mattwach/epaper_clock/src/clock_number_font.c

// Generated font data for clock_number_font

#include <inttypes.h>
#include <avr/pgmspace.h> 

const uint8_t clock_number_font[] PROGMEM = {
    0x56, 0x41, 0x52, 0x31,  // id: VAR1
    0x0C, // num_chars
    0x0A, // height

    // Character offsets
    ' ', 40, 0x00, 0x30,  // off=48
    '0', 40, 0x00, 0x38,  // off=56
    '1', 40, 0x00, 0xED,  // off=237
    '2', 40, 0x01, 0x36,  // off=310
    '3', 40, 0x01, 0xCC,  // off=460
    '4', 40, 0x02, 0x7D,  // off=637
    '5', 40, 0x02, 0xEE,  // off=750
    '6', 40, 0x03, 0x7F,  // off=895
    '7', 40, 0x04, 0x47,  // off=1095
    '8', 40, 0x04, 0xA1,  // off=1185
    '9', 40, 0x05, 0x77,  // off=1399
    ':', 16, 0x06, 0x42,  // off=1602
    // Character data
    // Character 32 (0x20) ( )
    // ----------------------------------------
    // ----------------------------------------
    // ----------------------------------------
    // ----------------------------------------
    // ----------------------------------------
    // ----------------------------------------
    // ----------------------------------------
    // ----------------------------------------
    // ----------------------------------------
    // ----------------------------------------
    // ----------------------------------------
    // ----------------------------------------
    // ----------------------------------------
    // ----------------------------------------
    // ----------------------------------------
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
    // ----------------------------------------
    // ----------------------------------------
    // ----------------------------------------
    // ----------------------------------------
    // ----------------------------------------
    // ----------------------------------------
    0x0A, 0x00, 0x81, 0x80, 0x02, 0xC0, 0x03, 0xE0, 0x08, 0xF0, 0x03, 0xE0, 0x02, 0xC0, 0x81, 0x80,
    0x0F, 0x00, 0x84, 0x80, 0xF0, 0xF8, 0xFC, 0x04, 0xFF, 0x83, 0x7F, 0x3F, 0x1F, 0x07, 0x0F, 0x02,
    0x1F, 0x82, 0x3F, 0x7F, 0x04, 0xFF, 0x84, 0xFE, 0xFC, 0xF8, 0x80, 0x09, 0x00, 0x82, 0x7E, 0x7F,
    0x04, 0xFF, 0x82, 0x1F, 0x01, 0x10, 0x00, 0x81, 0x01, 0x06, 0xFF, 0x81, 0xFC, 0x1F, 0x00, 0x82,
    0x80, 0xC0, 0x05, 0xFF, 0x82, 0x3F, 0x07, 0x1A, 0x00, 0x85, 0x80, 0xC0, 0xF0, 0xF8, 0xFE, 0x03,
    0xFF, 0x84, 0x7F, 0x1F, 0x07, 0x03, 0x15, 0x00, 0x84, 0x80, 0xC0, 0xE0, 0xF0, 0x02, 0xFC, 0x03,
    0xFF, 0x02, 0x3F, 0x83, 0x0F, 0x07, 0x03, 0x14, 0x00, 0x85, 0x80, 0xC0, 0xF0, 0xF8, 0xFC, 0x03,
    0xFF, 0x86, 0x7F, 0x3F, 0x0F, 0x07, 0x03, 0x01, 0x15, 0x00, 0x85, 0x80, 0xE0, 0xF8, 0xFC, 0xFE,
    0x02, 0xFF, 0x85, 0x7F, 0x3F, 0x1F, 0x03, 0x01, 0x1B, 0x00, 0x81, 0xFC, 0x07, 0xFF, 0x19, 0xFC,
    0x07, 0x00, 0x21, 0x03, 0x04, 0x00,
    // Character 51 (0x33) (3)
    // ----------------------------------------
    // ----------------------------------------
    // ----------------------------------------
    // ----------------------------------------
    // ----------------########----------------
    // -------------##############-------------
    // -----------##################-----------
    // ----------####################----------
    // ---------######################---------
    // --------########################--------
    // -------##########################-------
    // ------############################------
    // ------##########--------##########------
    // ------########-----------#########------
    // -----#########------------########------
    // -----########--------------########-----
    // ----########----------------#######-----
    // ----#######------------------######-----
    // ----#######------------------#######----
    // ----#######------------------#######----
    // ----#######------------------#######----
    // ----######-------------------#######----
    // ------####-------------------#######----
    // -----------------------------#######----
    // -----------------------------#######----
    // -----------------------------#######----
    // -----------------------------######-----
    // -----------------------------######-----
    // -----------------------------######-----
    // ----------------------------######------
    // ---------------------------#######------
    // --------------------------########------
    // --------------------------#######-------
    // ------------------------########--------
    // ---------------------##########---------
    // ---------------################---------
    // ---------------###############----------
    // ---------------#############------------
    // ---------------###########--------------
    // ---------------#############------------
    // ---------------###############----------
    // ---------------################---------
    // ---------------#################--------
    // ----------------------############------
    // -------------------------#########------
    // --------------------------#########-----
    // ----------------------------#######-----
    // -----------------------------#######----
    // -----------------------------#######----
    // ------------------------------######----
    // ------------------------------######----
    // -------------------------------######---
    // -------------------------------######---
    // -------------------------------######---
    // -------------------------------######---
    // ------###----------------------######---
    // ---######----------------------######---
    // ---#######---------------------######---
    // ---#######---------------------######---
    // ----######--------------------#######---
    // ----#######-------------------######----
    // ----#######------------------#######----
    // ----#######------------------#######----
    // ----########-----------------#######----
    // -----#########-------------#########----
    // -----#########------------#########-----
    // ------##########--------###########-----
    // ------############################------
    // -------###########################------
    // --------#########################-------
    // ---------#######################--------
    // ---------######################---------
    // -----------##################-----------
    // -------------###############------------
    // ----------------#########---------------
    // ----------------------------------------
    // ----------------------------------------
    // ----------------------------------------
    // ----------------------------------------
    // ----------------------------------------
    0x0A, 0x00, 0x81, 0x80, 0x02, 0xC0, 0x03, 0xE0, 0x08, 0xF0, 0x03, 0xE0, 0x02, 0xC0, 0x81, 0x80,
    0x0F, 0x00, 0x84, 0xC0, 0xF8, 0xFC, 0xFE, 0x04, 0xFF, 0x81, 0x7F, 0x02, 0x1F, 0x08, 0x0F, 0x83,
    0x1F, 0x3F, 0x7F, 0x04, 0xFF, 0x84, 0xFE, 0xFC, 0xF8, 0x80, 0x09, 0x00, 0x02, 0x3F, 0x04, 0x7F,
    0x82, 0x1F, 0x01, 0x10, 0x00, 0x81, 0x01, 0x06, 0xFF, 0x81, 0xFC, 0x1E, 0x00, 0x83, 0x80, 0xC0,
    0xE0, 0x05, 0xFF, 0x82, 0x1F, 0x03, 0x13, 0x00, 0x06, 0xF8, 0x03, 0xFC, 0x02, 0xFE, 0x02, 0xBF,
    0x02, 0x1F, 0x83, 0x0F, 0x03, 0x01, 0x16, 0x00, 0x07, 0x07, 0x03, 0x0F, 0x81, 0x1F, 0x02, 0x3F,
    0x84, 0x7F, 0xFF, 0xFE, 0xFC, 0x02, 0xF8, 0x82, 0xE0, 0x80, 0x0A, 0x00, 0x03, 0x80, 0x14, 0x00,
    0x82, 0x01, 0x07, 0x05, 0xFF, 0x81, 0xF8, 0x06, 0x00, 0x81, 0x07, 0x05, 0xFF, 0x83, 0xFE, 0xF0,
    0x80, 0x11, 0x00, 0x82, 0xE0, 0xF8, 0x05, 0xFF, 0x81, 0x0F, 0x08, 0x00, 0x84, 0x03, 0x0F, 0x1F,
    0x3F, 0x05, 0xFF, 0x02, 0xFC, 0x08, 0xF8, 0x02, 0xFC, 0x81, 0xFE, 0x04, 0xFF, 0x85, 0x7F, 0x3F,
    0x1F, 0x07, 0x01, 0x0F, 0x00, 0x02, 0x01, 0x03, 0x03, 0x09, 0x07, 0x03, 0x03, 0x81, 0x01, 0x0B,
    0x00,
    // Character 52 (0x34) (4)
    // ----------------------------------------
    // ----------------------------------------
    // ----------------------------------------
    // ----------------------------------------
    // ----------------------------------------
    // ------------------------#######---------
    // ------------------------#######---------
    // -----------------------########---------
    // -----------------------########---------
    // ----------------------#########---------
    // ---------------------##########---------
    // ---------------------##########---------
    // ---------------------##########---------
    // --------------------###########---------
    // -------------------############---------
    // -------------------############---------
    // -------------------#####-######---------
    // ------------------######-######---------
    // -----------------######--######---------
    // -----------------######--######---------
    // ----------------######---######---------
    // ----------------#####----######---------
    // ----------------#####----######---------
    // ---------------######----######---------
    // --------------######-----######---------
    // --------------#####------######---------
    // --------------#####------######---------
    // -------------######------######---------
    // ------------######-------######---------
    // ------------######-------######---------
    // -----------######--------######---------
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
    0x02, 0x3F, 0x81, 0x7F, 0x05, 0xFF, 0x84, 0xFC, 0xF8, 0xF0, 0xC0, 0x09, 0x00, 0x07, 0x03, 0x81,
    0x01, 0x0F, 0x00, 0x84, 0x01, 0x03, 0x1F, 0x7F, 0x05, 0xFF, 0x81, 0xC0, 0x22, 0x00, 0x06, 0xFF,
    0x06, 0x00, 0x81, 0x0C, 0x02, 0xFC, 0x03, 0xFE, 0x83, 0xF8, 0xE0, 0x80, 0x0F, 0x00, 0x83, 0x80,
    0xC0, 0xF8, 0x05, 0xFF, 0x81, 0x7F, 0x08, 0x00, 0x85, 0x01, 0x07, 0x1F, 0x3F, 0x7F, 0x04, 0xFF,
    0x81, 0xFE, 0x02, 0xFC, 0x07, 0xF8, 0x02, 0xFC, 0x81, 0xFE, 0x03, 0xFF, 0x02, 0x7F, 0x84, 0x1F,
    0x0F, 0x07, 0x01, 0x10, 0x00, 0x81, 0x01, 0x03, 0x03, 0x09, 0x07, 0x02, 0x03, 0x03, 0x01, 0x0B,
    0x00,
    // Character 54 (0x36) (6)
    // ----------------------------------------
    // ----------------------------------------
    // ----------------------------------------
    // ----------------------------------------
    // ------------------########--------------
    // ----------------############------------
    // --------------###############-----------
    // -------------##################---------
    // -----------####################---------
    // -----------#####################--------
    // ----------#######################-------
    // ---------#########################------
    // ---------##########-----##########------
    // ---------#######----------########------
    // --------#######-----------#########-----
    // -------#######-------------########-----
    // -------#######--------------#######-----
    // ------#######----------------#######----
    // ------#######----------------#######----
    // ------######-----------------##---------
    // ------#####-----------------------------
    // ------#####-----------------------------
    // -----######-----------------------------
    // -----######-----------------------------
    // -----######-----------------------------
    // -----######-----------------------------
    // ----######------------------------------
    // ----######------------------------------
    // ----######------------------------------
    // ----######---------#######--------------
    // ----######------############------------
    // ----#####-----###############-----------
    // ----#####----##################---------
    // ----#####---###################---------
    // ----#####--######################-------
    // ----#####--#######################------
    // ----#####-########################------
    // ----#####-#######-------##########------
    // ----###########-----------#########-----
    // ----##########------------#########-----
    // ----#########---------------########----
    // ----########-----------------#######----
    // ----#######------------------#######----
    // ----#######------------------#######----
    // ----#######-------------------######----
    // ----#######-------------------######----
    // ----######--------------------#######---
    // ----######---------------------######---
    // ----######---------------------######---
    // ----######---------------------######---
    // ----######---------------------######---
    // ----######---------------------######---
    // ----######---------------------######---
    // ----######---------------------######---
    // ----#######--------------------######---
    // -----######--------------------######---
    // -----######-------------------#######---
    // -----######-------------------######----
    // -----######-------------------######----
    // ------#####------------------#######----
    // ------######-----------------#######----
    // ------#######----------------#######----
    // ------########--------------########----
    // -------#######--------------#######-----
    // -------########-----------#########-----
    // --------########----------########------
    // --------##########------##########------
    // ---------#########################------
    // ---------########################-------
    // ----------######################--------
    // -----------####################---------
    // ------------##################----------
    // -------------################-----------
    // ---------------############-------------
    // -----------------########---------------
    // ----------------------------------------
    // ----------------------------------------
    // ----------------------------------------
    // ----------------------------------------
    // ----------------------------------------
    0x0D, 0x00, 0x81, 0x80, 0x02, 0xC0, 0x02, 0xE0, 0x08, 0xF0, 0x02, 0xE0, 0x81, 0xC0, 0x02, 0x80,
    0x10, 0x00, 0x84, 0x80, 0xC0, 0xF8, 0xFC, 0x03, 0xFF, 0x82, 0x7F, 0x3F, 0x03, 0x1F, 0x05, 0x0F,
    0x02, 0x1F, 0x81, 0x7F, 0x04, 0xFF, 0x84, 0xFE, 0xFC, 0xF8, 0xC0, 0x0A, 0x00, 0x82, 0xC0, 0xFE,
    0x04, 0xFF, 0x83, 0x0F, 0x07, 0x01, 0x0E, 0x00, 0x81, 0x01, 0x02, 0x0F, 0x04, 0x07, 0x81, 0x06,
    0x08, 0x00, 0x81, 0xFC, 0x04, 0xFF, 0x82, 0x7F, 0x03, 0x03, 0x00, 0x02, 0x80, 0x03, 0xC0, 0x07,
    0xE0, 0x02, 0xC0, 0x81, 0x80, 0x0F, 0x00, 0x05, 0xFF, 0x86, 0xC0, 0xF0, 0xFC, 0xFE, 0xFF, 0x7F,
    0x02, 0x3F, 0x07, 0x1F, 0x02, 0x3F, 0x05, 0xFF, 0x02, 0xFC, 0x82, 0xF8, 0xC0, 0x09, 0x00, 0x06,
    0xFF, 0x83, 0x3F, 0x03, 0x01, 0x0F, 0x00, 0x83, 0x01, 0x0F, 0x7F, 0x05, 0xFF, 0x81, 0xC0, 0x07,
    0x00, 0x81, 0x7F, 0x05, 0xFF, 0x81, 0xC0, 0x14, 0x00, 0x06, 0xFF, 0x08, 0x00, 0x82, 0x07, 0x7F,
    0x04, 0xFF, 0x83, 0xF0, 0xE0, 0xC0, 0x0E, 0x00, 0x82, 0xC0, 0xF8, 0x05, 0xFF, 0x82, 0x7F, 0x01,
    0x0A, 0x00, 0x85, 0x01, 0x07, 0x1F, 0x3F, 0x7F, 0x03, 0xFF, 0x81, 0xFE, 0x02, 0xFC, 0x06, 0xF8,
    0x02, 0xFC, 0x04, 0xFF, 0x85, 0x7F, 0x3F, 0x1F, 0x0F, 0x01, 0x12, 0x00, 0x02, 0x01, 0x02, 0x03,
    0x08, 0x07, 0x02, 0x03, 0x02, 0x01, 0x0B, 0x00,
    // Character 55 (0x37) (7)
    // ----------------------------------------
    // ----------------------------------------
    // ----------------------------------------
    // ----------------------------------------
    // ----------------------------------------
    // ----################################----
    // ----################################----
    // ----################################----
    // ----################################----
    // ----################################----
    // ----################################----
    // ----################################----
    // ----################################----
    // ------------------------------######----
    // -----------------------------#######----
    // -----------------------------######-----
    // -----------------------------#####------
    // ----------------------------######------
    // ---------------------------#######------
    // ---------------------------######-------
    // --------------------------#######-------
    // --------------------------######--------
    // --------------------------######--------
    // -------------------------######---------
    // ------------------------#######---------
    // ------------------------#######---------
    // ------------------------######----------
    // ------------------------######----------
    // -----------------------######-----------
    // -----------------------######-----------
    // ----------------------#######-----------
    // ---------------------#######------------
    // ---------------------#######------------
    // ---------------------######-------------
    // ---------------------######-------------
    // --------------------######--------------
    // --------------------######--------------
    // -------------------#######--------------
    // -------------------#######--------------
    // -------------------######---------------
    // -------------------######---------------
    // -------------------######---------------
    // ------------------######----------------
    // ------------------######----------------
    // -----------------#######----------------
    // -----------------#######----------------
    // -----------------######-----------------
    // ----------------#######-----------------
    // ----------------#######-----------------
    // ----------------######------------------
    // ----------------######------------------
    // ----------------######------------------
    // ---------------######-------------------
    // ---------------######-------------------
    // ---------------######-------------------
    // ---------------######-------------------
    // --------------#######-------------------
    // --------------#######-------------------
    // --------------#######-------------------
    // --------------#######-------------------
    // --------------######--------------------
    // --------------######--------------------
    // --------------######--------------------
    // --------------######--------------------
    // --------------######--------------------
    // --------------######--------------------
    // -------------######---------------------
    // -------------######---------------------
    // -------------######---------------------
    // -------------######---------------------
    // -------------######---------------------
    // -------------######---------------------
    // -------------######---------------------
    // -------------######---------------------
    // ----------------------------------------
    // ----------------------------------------
    // ----------------------------------------
    // ----------------------------------------
    // ----------------------------------------
    // ----------------------------------------
    0x04, 0x00, 0x20, 0xE0, 0x08, 0x00, 0x19, 0x1F, 0x81, 0xDF, 0x05, 0xFF, 0x81, 0x7F, 0x1D, 0x00,
    0x84, 0x80, 0xF0, 0xFC, 0xFE, 0x02, 0xFF, 0x83, 0x7F, 0x1F, 0x07, 0x1B, 0x00, 0x83, 0x80, 0xC0,
    0xF0, 0x04, 0xFF, 0x83, 0x7F, 0x0F, 0x03, 0x1C, 0x00, 0x82, 0xE0, 0xF8, 0x04, 0xFF, 0x83, 0x7F,
    0x07, 0x01, 0x1C, 0x00, 0x83, 0x80, 0xF0, 0xFC, 0x04, 0xFF, 0x82, 0x3F, 0x03, 0x1E, 0x00, 0x81,
    0xF0, 0x05, 0xFF, 0x82, 0x0F, 0x01, 0x1F, 0x00, 0x06, 0xFF, 0x81, 0x0F, 0x20, 0x00, 0x81, 0xFC,
    0x05, 0xFF, 0x81, 0x03, 0x21, 0x00, 0x06, 0x03, 0x15, 0x00,
    // Character 56 (0x38) (8)
    // ----------------------------------------
    // ----------------------------------------
    // ----------------------------------------
    // ----------------------------------------
    // ----------------########----------------
    // -------------##############-------------
    // -----------##################-----------
    // ----------####################----------
    // ---------######################---------
    // --------########################--------
    // -------##########################-------
    // -------##########################-------
    // ------##########--------##########------
    // ------########------------########------
    // ------########------------########------
    // -----########--------------########-----
    // -----#######----------------#######-----
    // -----######------------------######-----
    // ----#######------------------#######----
    // ----#######------------------#######----
    // ----#######------------------#######----
    // ----#######------------------#######----
    // ----#######------------------#######----
    // ----#######------------------#######----
    // ----#######------------------#######----
    // ----#######------------------#######----
    // -----######------------------######-----
    // -----######------------------######-----
    // -----######------------------######-----
    // ------######----------------######------
    // ------#######--------------#######------
    // ------########------------########------
    // -------########-----------#######-------
    // -------#########--------#########-------
    // --------########################--------
    // ---------######################---------
    // ----------####################----------
    // -----------#################------------
    // ------------################------------
    // ----------####################----------
    // ---------######################---------
    // --------#########################-------
    // ------##########--------##########------
    // ------########------------########------
    // -----########--------------########-----
    // -----#######-----------------######-----
    // ----#######------------------#######----
    // ----#######------------------#######----
    // ----######--------------------######----
    // ----######--------------------######----
    // ---#######---------------------######---
    // ---######----------------------######---
    // ---######----------------------######---
    // ---######----------------------######---
    // ---######----------------------######---
    // ---######----------------------######---
    // ---######----------------------######---
    // ---######----------------------######---
    // ---#######--------------------#######---
    // ---#######--------------------#######---
    // ----######--------------------######----
    // ----#######------------------#######----
    // ----#######------------------#######----
    // ----########-----------------#######----
    // ----#########--------------#########----
    // -----#########------------#########-----
    // -----###########--------###########-----
    // ------############################------
    // ------############################------
    // -------##########################-------
    // --------########################--------
    // ---------######################---------
    // -----------##################-----------
    // ------------################------------
    // ----------------########----------------
    // ----------------------------------------
    // ----------------------------------------
    // ----------------------------------------
    // ----------------------------------------
    // ----------------------------------------
    0x0A, 0x00, 0x81, 0x80, 0x02, 0xC0, 0x03, 0xE0, 0x08, 0xF0, 0x03, 0xE0, 0x02, 0xC0, 0x81, 0x80,
    0x0F, 0x00, 0x84, 0x80, 0xF0, 0xFC, 0xFE, 0x04, 0xFF, 0x81, 0x7F, 0x02, 0x1F, 0x08, 0x0F, 0x02,
    0x1F, 0x81, 0x7F, 0x04, 0xFF, 0x84, 0xFE, 0xFC, 0xF0, 0x80, 0x09, 0x00, 0x81, 0xFC, 0x06, 0xFF,
    0x81, 0x01, 0x10, 0x00, 0x81, 0x01, 0x06, 0xFF, 0x81, 0xFC, 0x08, 0x00, 0x82, 0x03, 0x1F, 0x05,
    0xFF, 0x83, 0xE0, 0xC0, 0x80, 0x0C, 0x00, 0x83, 0x80, 0xC0, 0xE0, 0x05, 0xFF, 0x82, 0x1F, 0x03,
    0x0B, 0x00, 0x85, 0x03, 0x07, 0x0F, 0x9F, 0xBF, 0x03, 0xFF, 0x81, 0xFE, 0x08, 0xFC, 0x02, 0xFE,
    0x02, 0xFF, 0x02, 0x9F, 0x83, 0x0F, 0x07, 0x03, 0x0B, 0x00, 0x82, 0xC0, 0xF0, 0x02, 0xFC, 0x81,
    0xFE, 0x02, 0xFF, 0x83, 0x3F, 0x1F, 0x0F, 0x02, 0x07, 0x08, 0x03, 0x02, 0x07, 0x81, 0x0F, 0x02,
    0x1F, 0x02, 0xFF, 0x02, 0xFE, 0x83, 0xFC, 0xF0, 0xC0, 0x07, 0x00, 0x81, 0xFC, 0x05, 0xFF, 0x81,
    0x07, 0x14, 0x00, 0x81, 0x03, 0x05, 0xFF, 0x81, 0xFC, 0x06, 0x00, 0x81, 0x0F, 0x05, 0xFF, 0x83,
    0xFC, 0xE0, 0x80, 0x11, 0x00, 0x82, 0xE0, 0xFC, 0x05, 0xFF, 0x81, 0x0F, 0x07, 0x00, 0x85, 0x01,
    0x07, 0x1F, 0x3F, 0x7F, 0x04, 0xFF, 0x81, 0xFE, 0x02, 0xFC, 0x08, 0xF8, 0x02, 0xFC, 0x81, 0xFE,
    0x04, 0xFF, 0x85, 0x7F, 0x3F, 0x1F, 0x07, 0x01, 0x0F, 0x00, 0x81, 0x01, 0x04, 0x03, 0x08, 0x07,
    0x04, 0x03, 0x81, 0x01, 0x0B, 0x00,
    // Character 57 (0x39) (9)
    // ----------------------------------------
    // ----------------------------------------
    // ----------------------------------------
    // ----------------------------------------
    // ----------------########----------------
    // -------------#############--------------
    // -----------################-------------
    // ----------###################-----------
    // ---------####################-----------
    // --------######################----------
    // -------########################---------
    // ------#########################---------
    // ------##########------##########--------
    // ------########----------#########-------
    // -----#########-----------########-------
    // ----########--------------########------
    // ----#######----------------#######------
    // ----#######----------------#######------
    // ----#######-----------------######------
    // ----#######------------------#####------
    // ----######-------------------######-----
    // ---#######-------------------######-----
    // ---#######-------------------######-----
    // ---######--------------------#######----
    // ---######---------------------######----
    // ---######---------------------######----
    // ---######---------------------######----
    // ---######---------------------######----
    // ---######---------------------######----
    // ---######---------------------######----
    // ---######---------------------######----
    // ---#######--------------------######----
    // ---#######--------------------######----
    // ----######-------------------#######----
    // ----#######------------------#######----
    // ----#######------------------#######----
    // ----#######------------------#######----
    // ----########----------------########----
    // ----########---------------#########----
    // -----#########------------##########----
    // -----#########----------############----
    // ------##########------########-#####----
    // ------#######################--#####----
    // -------######################--#####----
    // --------#####################--#####----
    // ---------##################----#####----
    // ---------#################----######----
    // -----------##############-----######----
    // ------------############------######----
    // --------------#######---------######----
    // ------------------------------######----
    // ------------------------------######----
    // -----------------------------#######----
    // -----------------------------######-----
    // -----------------------------######-----
    // -----------------------------######-----
    // -----------------------------######-----
    // -----------------------------#####------
    // ----------------------------######------
    // --------##------------------######------
    // ----#######----------------#######------
    // ----#######---------------########------
    // ----#######---------------#######-------
    // ----########-------------#######--------
    // ----#########-----------########--------
    // -----#########---------########---------
    // ------##########-----##########---------
    // ------#########################---------
    // ------########################----------
    // -------######################-----------
    // --------####################------------
    // ---------##################-------------
    // ----------################--------------
    // -----------#############----------------
    // --------------########------------------
    // ----------------------------------------
    // ----------------------------------------
    // ----------------------------------------
    // ----------------------------------------
    // ----------------------------------------
    0x0A, 0x00, 0x81, 0x80, 0x02, 0xC0, 0x03, 0xE0, 0x08, 0xF0, 0x02, 0xE0, 0x81, 0xC0, 0x02, 0x80,
    0x0F, 0x00, 0x85, 0x80, 0xC0, 0xF8, 0xFC, 0xFE, 0x03, 0xFF, 0x02, 0x7F, 0x02, 0x1F, 0x06, 0x0F,
    0x02, 0x1F, 0x82, 0x3F, 0x7F, 0x03, 0xFF, 0x85, 0xFE, 0xFC, 0xF0, 0xE0, 0x80, 0x09, 0x00, 0x81,
    0xE0, 0x05, 0xFF, 0x82, 0x7F, 0x0F, 0x10, 0x00, 0x82, 0x03, 0x07, 0x05, 0xFF, 0x82, 0xF0, 0x80,
    0x07, 0x00, 0x06, 0xFF, 0x81, 0x80, 0x14, 0x00, 0x06, 0xFF, 0x07, 0x00, 0x82, 0x01, 0x7F, 0x05,
    0xFF, 0x82, 0xFC, 0xE0, 0x02, 0x80, 0x0C, 0x00, 0x84, 0x80, 0xC0, 0xE0, 0xFE, 0x06, 0xFF, 0x09,
    0x00, 0x84, 0x01, 0x07, 0x0F, 0x1F, 0x02, 0x7F, 0x03, 0xFF, 0x02, 0xFE, 0x06, 0xFC, 0x02, 0xFE,
    0x83, 0xFF, 0x7F, 0x3F, 0x02, 0x1F, 0x82, 0x03, 0xC1, 0x05, 0xFF, 0x10, 0x00, 0x02, 0x01, 0x07,
    0x03, 0x03, 0x01, 0x05, 0x00, 0x81, 0xF0, 0x05, 0xFF, 0x81, 0x1F, 0x08, 0x00, 0x04, 0xF0, 0x02,
    0xF8, 0x82, 0xF0, 0x80, 0x0D, 0x00, 0x84, 0x80, 0xE0, 0xF0, 0xFC, 0x03, 0xFF, 0x83, 0x7F, 0x3F,
    0x01, 0x09, 0x00, 0x85, 0x01, 0x03, 0x1F, 0x3F, 0x7F, 0x04, 0xFF, 0x81, 0xFE, 0x02, 0xFC, 0x05,
    0xF8, 0x02, 0xFC, 0x81, 0xFE, 0x03, 0xFF, 0x85, 0x7F, 0x3F, 0x1F, 0x0F, 0x01, 0x12, 0x00, 0x81,
    0x01, 0x03, 0x03, 0x08, 0x07, 0x02, 0x03, 0x02, 0x01, 0x0E, 0x00,
    // Character 58 (0x3A) (:)
    // ----------------
    // ----------------
    // ----------------
    // ----------------
    // ----------------
    // ----------------
    // ----------------
    // ----------------
    // ----------------
    // ----------------
    // ----------------
    // ----------------
    // ----------------
    // ----------------
    // ----------------
    // ----------------
    // ----------------
    // ----------------
    // ----------------
    // ---#########----
    // ---#########----
    // ---#########----
    // ---#########----
    // ---#########----
    // ---#########----
    // ---#########----
    // ---#########----
    // ---#########----
    // ---#########----
    // ---#########----
    // ---#########----
    // ---#########----
    // ---#########----
    // ---#########----
    // ----------------
    // ----------------
    // ----------------
    // ----------------
    // ----------------
    // ----------------
    // ----------------
    // ----------------
    // ----------------
    // ----------------
    // ----------------
    // ----------------
    // ----------------
    // ----------------
    // ----------------
    // ----------------
    // ----------------
    // ----------------
    // ----------------
    // ----------------
    // ----------------
    // ----------------
    // ----------------
    // ----------------
    // ----------------
    // ---#########----
    // ---#########----
    // ---#########----
    // ---#########----
    // ---#########----
    // ---#########----
    // ---#########----
    // ---#########----
    // ---#########----
    // ---#########----
    // ---#########----
    // ---#########----
    // ---#########----
    // ---#########----
    // ---#########----
    // ----------------
    // ----------------
    // ----------------
    // ----------------
    // ----------------
    // ----------------
    0x23, 0x00, 0x09, 0xF8, 0x07, 0x00, 0x09, 0xFF, 0x07, 0x00, 0x09, 0x03, 0x27, 0x00, 0x09, 0xF8,
    0x07, 0x00, 0x09, 0xFF, 0x07, 0x00, 0x09, 0x03, 0x04, 0x00,
};
