mattwach/epaper_clock/src/labels_font.c

// Generated font data for labels_font

#include <inttypes.h>
#include <avr/pgmspace.h> 

const uint8_t labels_font[] PROGMEM = {
    0x56, 0x41, 0x52, 0x31,  // id: VAR1
    0x11, // num_chars
    0x03, // height

    // Character offsets
    ' ', 9, 0x00, 0x44,  // off=68
    '%', 19, 0x00, 0x46,  // off=70
    '.', 6, 0x00, 0x7D,  // off=125
    '/', 8, 0x00, 0x83,  // off=131
    ':', 6, 0x00, 0x97,  // off=151
    'A', 14, 0x00, 0xA1,  // off=161
    'C', 15, 0x00, 0xBE,  // off=190
    'F', 12, 0x00, 0xE5,  // off=229
    'H', 12, 0x00, 0xF7,  // off=247
    'M', 15, 0x01, 0x11,  // off=273
    'P', 13, 0x01, 0x3D,  // off=317
    'T', 14, 0x01, 0x56,  // off=342
    'U', 14, 0x01, 0x68,  // off=360
    'h', 11, 0x01, 0x88,  // off=392
    'i', 5, 0x01, 0xA2,  // off=418
    'n', 11, 0x01, 0xB0,  // off=432
    'r', 8, 0x01, 0xC6,  // off=454
    // Character data
    // Character 32 (0x20) ( )
    // ---------
    // ---------
    // ---------
    // ---------
    // ---------
    // ---------
    // ---------
    // ---------
    // ---------
    // ---------
    // ---------
    // ---------
    // ---------
    // ---------
    // ---------
    // ---------
    // ---------
    // ---------
    // ---------
    // ---------
    // ---------
    // ---------
    // ---------
    // ---------
    0x1B, 0x00,
    // Character 37 (0x25) (%)
    // -------------------
    // -------------------
    // -------------------
    // -------------------
    // -------------------
    // -------------------
    // --####-------##----
    // -##--##-----##-----
    // -#----#-----#------
    // -#----#----##------
    // -#----#---##-------
    // -#----#---#--------
    // -##--##--##--####--
    // --####--##--##--##-
    // --------#---#----#-
    // -------##---#----#-
    // ------##----#----#-
    // ------#-----#----#-
    // -----##-----##--##-
    // ----##-------####--
    // -------------------
    // -------------------
    // -------------------
    // -------------------
    0x83, 0x00, 0x80, 0xC0, 0x02, 0x40, 0x82, 0xC0, 0x80, 0x05, 0x00, 0x83, 0x80, 0xC0, 0x40, 0x05,
    0x00, 0x82, 0x1F, 0x30, 0x02, 0x20, 0x89, 0x30, 0x1F, 0x80, 0xE0, 0x30, 0x1C, 0x06, 0xE3, 0x30,
    0x02, 0x10, 0x82, 0x30, 0xE0, 0x05, 0x00, 0x84, 0x08, 0x0C, 0x07, 0x01, 0x04, 0x00, 0x82, 0x07,
    0x0C, 0x02, 0x08, 0x83, 0x0C, 0x07, 0x00,
    // Character 46 (0x2E) (.)
    // ------
    // ------
    // ------
    // ------
    // ------
    // ------
    // ------
    // ------
    // ------
    // ------
    // ------
    // ------
    // ------
    // ------
    // ------
    // ------
    // ------
    // ------
    // --##--
    // --##--
    // ------
    // ------
    // ------
    // ------
    0x0E, 0x00, 0x02, 0x0C, 0x02, 0x00,
    // Character 47 (0x2F) (/)
    // --------
    // --------
    // --------
    // --------
    // --------
    // -----##-
    // -----##-
    // -----#--
    // ----##--
    // ----##--
    // ----#---
    // ---##---
    // ---##---
    // ---##---
    // ---#----
    // --##----
    // --##----
    // --#-----
    // -##-----
    // -##-----
    // --------
    // --------
    // --------
    // --------
    0x05, 0x00, 0x82, 0xE0, 0x60, 0x03, 0x00, 0x84, 0x80, 0xF8, 0x3F, 0x03, 0x03, 0x00, 0x83, 0x0C,
    0x0F, 0x01, 0x04, 0x00,
    // Character 58 (0x3A) (:)
    // ------
    // ------
    // ------
    // ------
    // ------
    // ------
    // ------
    // ------
    // ------
    // --##--
    // --##--
    // ------
    // ------
    // ------
    // ------
    // ------
    // ------
    // ------
    // --##--
    // --##--
    // ------
    // ------
    // ------
    // ------
    0x08, 0x00, 0x02, 0x06, 0x04, 0x00, 0x02, 0x0C, 0x02, 0x00,
    // Character 65 (0x41) (A)
    // --------------
    // --------------
    // --------------
    // --------------
    // --------------
    // --------------
    // -----###------
    // -----###------
    // ----##-##-----
    // ----##-##-----
    // ----#---#-----
    // ---##---##----
    // ---##---##----
    // ---#-----#----
    // --#########---
    // --#-------#---
    // -##-------##--
    // -##-------##--
    // -##--------#--
    // ##---------##-
    // --------------
    // --------------
    // --------------
    // --------------
    0x05, 0x00, 0x03, 0xC0, 0x08, 0x00, 0x89, 0xC0, 0x78, 0x5F, 0x43, 0x40, 0x43, 0x5F, 0x78, 0xC0,
    0x03, 0x00, 0x83, 0x08, 0x0F, 0x07, 0x07, 0x00, 0x84, 0x03, 0x0F, 0x08, 0x00,
    // Character 67 (0x43) (C)
    // ---------------
    // ---------------
    // ---------------
    // ---------------
    // ---------------
    // ---------------
    // -----######----
    // ---###----###--
    // --##-------###-
    // --##--------##-
    // -##------------
    // -##------------
    // -##------------
    // -##------------
    // -##------------
    // -##------------
    // --##--------##-
    // --###-------##-
    // ---###----###--
    // -----######----
    // ---------------
    // ---------------
    // ---------------
    // ---------------
    0x03, 0x00, 0x02, 0x80, 0x81, 0xC0, 0x04, 0x40, 0x81, 0xC0, 0x02, 0x80, 0x03, 0x00, 0x83, 0xFC,
    0xFF, 0x03, 0x07, 0x00, 0x81, 0x01, 0x02, 0x03, 0x03, 0x00, 0x84, 0x03, 0x07, 0x06, 0x0C, 0x04,
    0x08, 0x85, 0x0C, 0x04, 0x07, 0x03, 0x00,
    // Character 70 (0x46) (F)
    // ------------
    // ------------
    // ------------
    // ------------
    // ------------
    // ------------
    // -##########-
    // -##---------
    // -##---------
    // -##---------
    // -##---------
    // -##---------
    // -##---------
    // -##########-
    // -##---------
    // -##---------
    // -##---------
    // -##---------
    // -##---------
    // -##---------
    // ------------
    // ------------
    // ------------
    // ------------
    0x81, 0x00, 0x02, 0xC0, 0x08, 0x40, 0x02, 0x00, 0x02, 0xFF, 0x08, 0x20, 0x02, 0x00, 0x02, 0x0F,
    0x09, 0x00,
    // Character 72 (0x48) (H)
    // ------------
    // ------------
    // ------------
    // ------------
    // ------------
    // ------------
    // -##------##-
    // -##------##-
    // -##------##-
    // -##------##-
    // -##------##-
    // -##------##-
    // -##########-
    // -##------##-
    // -##------##-
    // -##------##-
    // -##------##-
    // -##------##-
    // -##------##-
    // -##------##-
    // ------------
    // ------------
    // ------------
    // ------------
    0x81, 0x00, 0x02, 0xC0, 0x06, 0x00, 0x02, 0xC0, 0x02, 0x00, 0x02, 0xFF, 0x06, 0x10, 0x02, 0xFF,
    0x02, 0x00, 0x02, 0x0F, 0x06, 0x00, 0x02, 0x0F, 0x01, 0x00,
    // Character 77 (0x4D) (M)
    // ---------------
    // ---------------
    // ---------------
    // ---------------
    // ---------------
    // ---------------
    // -##---------##-
    // -###-------###-
    // -#-#-------#-#-
    // -#-##------#-#-
    // -#-##-----##-#-
    // -#--#-----#--#-
    // -#--##---##--#-
    // -#--##---##--#-
    // -#---##--#---#-
    // -#---##-##---#-
    // -#----#-##---#-
    // -#----#-#----#-
    // -#----###----#-
    // -#-----#-----#-
    // ---------------
    // ---------------
    // ---------------
    // ---------------
    0x81, 0x00, 0x02, 0xC0, 0x81, 0x80, 0x07, 0x00, 0x81, 0x80, 0x02, 0xC0, 0x02, 0x00, 0x8D, 0xFF,
    0x00, 0x07, 0x3E, 0xF0, 0xC0, 0x00, 0x80, 0xF0, 0x3C, 0x07, 0x00, 0xFF, 0x02, 0x00, 0x81, 0x0F,
    0x04, 0x00, 0x84, 0x07, 0x0C, 0x07, 0x01, 0x03, 0x00, 0x82, 0x0F, 0x00,
    // Character 80 (0x50) (P)
    // -------------
    // -------------
    // -------------
    // -------------
    // -------------
    // -------------
    // -#########---
    // -##------##--
    // -##-------##-
    // -##-------##-
    // -##-------##-
    // -##-------##-
    // -##------##--
    // -#########---
    // -##----------
    // -##----------
    // -##----------
    // -##----------
    // -##----------
    // -##----------
    // -------------
    // -------------
    // -------------
    // -------------
    0x81, 0x00, 0x02, 0xC0, 0x06, 0x40, 0x82, 0xC0, 0x80, 0x03, 0x00, 0x02, 0xFF, 0x06, 0x20, 0x83,
    0x30, 0x1F, 0x0F, 0x02, 0x00, 0x02, 0x0F, 0x0A, 0x00,
    // Character 84 (0x54) (T)
    // --------------
    // --------------
    // --------------
    // --------------
    // --------------
    // --------------
    // -############-
    // ------##------
    // ------##------
    // ------##------
    // ------##------
    // ------##------
    // ------##------
    // ------##------
    // ------##------
    // ------##------
    // ------##------
    // ------##------
    // ------##------
    // ------##------
    // --------------
    // --------------
    // --------------
    // --------------
    0x81, 0x00, 0x05, 0x40, 0x02, 0xC0, 0x05, 0x40, 0x07, 0x00, 0x02, 0xFF, 0x0C, 0x00, 0x02, 0x0F,
    0x06, 0x00,
    // Character 85 (0x55) (U)
    // --------------
    // --------------
    // --------------
    // --------------
    // --------------
    // --------------
    // -##--------##-
    // -##--------##-
    // -##--------##-
    // -##--------##-
    // -##--------##-
    // -##--------##-
    // -##--------##-
    // -##--------##-
    // -##--------##-
    // --#--------#--
    // --##------##--
    // --##------##--
    // ---##----##---
    // ----######----
    // --------------
    // --------------
    // --------------
    // --------------
    0x81, 0x00, 0x02, 0xC0, 0x08, 0x00, 0x02, 0xC0, 0x02, 0x00, 0x82, 0x7F, 0xFF, 0x08, 0x00, 0x82,
    0xFF, 0x7F, 0x03, 0x00, 0x83, 0x03, 0x07, 0x0C, 0x04, 0x08, 0x83, 0x0C, 0x07, 0x03, 0x02, 0x00,
    // Character 104 (0x68) (h)
    // -----------
    // -----------
    // -----------
    // -----------
    // -----------
    // -##--------
    // -##--------
    // -##--------
    // -##--------
    // -##-####---
    // -###---##--
    // -###----##-
    // -##-----##-
    // -##-----##-
    // -##-----##-
    // -##-----##-
    // -##-----##-
    // -##-----##-
    // -##-----##-
    // -##-----##-
    // -----------
    // -----------
    // -----------
    // -----------
    0x81, 0x00, 0x02, 0xE0, 0x09, 0x00, 0x02, 0xFF, 0x81, 0x0C, 0x03, 0x02, 0x83, 0x06, 0xFC, 0xF8,
    0x02, 0x00, 0x02, 0x0F, 0x05, 0x00, 0x02, 0x0F, 0x01, 0x00,
    // Character 105 (0x69) (i)
    // -----
    // -----
    // -----
    // -----
    // -----
    // -##--
    // -##--
    // -----
    // -----
    // -##--
    // -##--
    // -##--
    // -##--
    // -##--
    // -##--
    // -##--
    // -##--
    // -##--
    // -##--
    // -##--
    // -----
    // -----
    // -----
    // -----
    0x81, 0x00, 0x02, 0x60, 0x03, 0x00, 0x02, 0xFE, 0x03, 0x00, 0x02, 0x0F, 0x02, 0x00,
    // Character 110 (0x6E) (n)
    // -----------
    // -----------
    // -----------
    // -----------
    // -----------
    // -----------
    // -----------
    // -----------
    // -----------
    // -##-####---
    // -###---##--
    // -###----##-
    // -##-----##-
    // -##-----##-
    // -##-----##-
    // -##-----##-
    // -##-----##-
    // -##-----##-
    // -##-----##-
    // -##-----##-
    // -----------
    // -----------
    // -----------
    // -----------
    0x0C, 0x00, 0x02, 0xFE, 0x81, 0x0C, 0x03, 0x02, 0x83, 0x06, 0xFC, 0xF8, 0x02, 0x00, 0x02, 0x0F,
    0x05, 0x00, 0x02, 0x0F, 0x01, 0x00,
    // Character 114 (0x72) (r)
    // --------
    // --------
    // --------
    // --------
    // --------
    // --------
    // --------
    // --------
    // --------
    // -##-###-
    // -##-###-
    // -###----
    // -###----
    // -##-----
    // -##-----
    // -##-----
    // -##-----
    // -##-----
    // -##-----
    // -##-----
    // --------
    // --------
    // --------
    // --------
    0x09, 0x00, 0x02, 0xFE, 0x81, 0x18, 0x03, 0x06, 0x02, 0x00, 0x02, 0x0F, 0x05, 0x00,
};
