mattwach/epaper_clock/src/pressure_font.c

// Generated font data for pressure_font

#include <inttypes.h>
#include <avr/pgmspace.h> 

const uint8_t pressure_font[] PROGMEM = {
    0x56, 0x41, 0x52, 0x31,  // id: VAR1
    0x28, // num_chars
    0x02, // height

    // Character offsets
    ' ', 9, 0x00, 0xA0,  // off=160
    '+', 9, 0x00, 0xA2,  // off=162
    '-', 9, 0x00, 0xB0,  // off=176
    '.', 5, 0x00, 0xB6,  // off=182
    '0', 9, 0x00, 0xBC,  // off=188
    '1', 9, 0x00, 0xD1,  // off=209
    '2', 9, 0x00, 0xE1,  // off=225
    '3', 9, 0x00, 0xF4,  // off=244
    '4', 9, 0x01, 0x08,  // off=264
    '5', 9, 0x01, 0x1D,  // off=285
    '6', 9, 0x01, 0x2F,  // off=303
    '7', 9, 0x01, 0x42,  // off=322
    '8', 9, 0x01, 0x52,  // off=338
    '9', 9, 0x01, 0x63,  // off=355
    ':', 9, 0x01, 0x76,  // off=374
    'A', 10, 0x01, 0x80,  // off=384
    'C', 9, 0x01, 0x98,  // off=408
    'D', 9, 0x01, 0xAD,  // off=429
    'E', 9, 0x01, 0xBF,  // off=447
    'F', 9, 0x01, 0xCD,  // off=461
    'G', 9, 0x01, 0xDA,  // off=474
    'H', 9, 0x01, 0xEF,  // off=495
    'I', 9, 0x01, 0xFF,  // off=511
    'K', 9, 0x02, 0x0F,  // off=527
    'L', 9, 0x02, 0x23,  // off=547
    'M', 10, 0x02, 0x2D,  // off=557
    'N', 9, 0x02, 0x45,  // off=581
    'O', 9, 0x02, 0x5B,  // off=603
    'P', 9, 0x02, 0x70,  // off=624
    'R', 9, 0x02, 0x80,  // off=640
    'S', 9, 0x02, 0x92,  // off=658
    'T', 9, 0x02, 0xA5,  // off=677
    'U', 9, 0x02, 0xB1,  // off=689
    'Z', 9, 0x02, 0xC2,  // off=706
    'a', 10, 0x02, 0xD5,  // off=725
    'h', 9, 0x02, 0xEA,  // off=746
    'i', 9, 0x02, 0xFC,  // off=764
    'm', 9, 0x03, 0x0C,  // off=780
    'n', 9, 0x03, 0x22,  // off=802
    'x', 9, 0x03, 0x34,  // off=820
    // Character data
    // Character 32 (0x20) ( )
    // ---------
    // ---------
    // ---------
    // ---------
    // ---------
    // ---------
    // ---------
    // ---------
    // ---------
    // ---------
    // ---------
    // ---------
    // ---------
    // ---------
    // ---------
    // ---------
    0x12, 0x00,
    // Character 43 (0x2B) (+)
    // ---------
    // ---------
    // ---------
    // ---------
    // ---------
    // ---##----
    // ---##----
    // ---##----
    // ########-
    // ########-
    // ---##----
    // ---##----
    // ---##----
    // ---------
    // ---------
    // ---------
    0x03, 0x00, 0x02, 0xE0, 0x04, 0x00, 0x03, 0x03, 0x02, 0x1F, 0x03, 0x03, 0x01, 0x00,
    // Character 45 (0x2D) (-)
    // ---------
    // ---------
    // ---------
    // ---------
    // ---------
    // ---------
    // ---------
    // ---------
    // --####---
    // --####---
    // ---------
    // ---------
    // ---------
    // ---------
    // ---------
    // ---------
    0x0B, 0x00, 0x04, 0x03, 0x03, 0x00,
    // Character 46 (0x2E) (.)
    // -----
    // -----
    // -----
    // -----
    // -----
    // -----
    // -----
    // -----
    // -----
    // -----
    // -----
    // -----
    // -##--
    // -##--
    // -----
    // -----
    0x06, 0x00, 0x02, 0x30, 0x02, 0x00,
    // Character 48 (0x30) (0)
    // ---------
    // ---------
    // ---------
    // --####---
    // -######--
    // ###--###-
    // ##----##-
    // ##-##-##-
    // ##-##-##-
    // ##----##-
    // ##----##-
    // ###--###-
    // -######--
    // --####---
    // ---------
    // ---------
    0x83, 0xE0, 0xF0, 0x38, 0x02, 0x98, 0x87, 0x38, 0xF0, 0xE0, 0x00, 0x0F, 0x1F, 0x38, 0x02, 0x31,
    0x84, 0x38, 0x1F, 0x0F, 0x00,
    // Character 49 (0x31) (1)
    // ---------
    // ---------
    // ---------
    // ---##----
    // --###----
    // #####----
    // ##-##----
    // ---##----
    // ---##----
    // ---##----
    // ---##----
    // ---##----
    // ########-
    // ########-
    // ---------
    // ---------
    0x02, 0x60, 0x81, 0x30, 0x02, 0xF8, 0x04, 0x00, 0x03, 0x30, 0x02, 0x3F, 0x03, 0x30, 0x01, 0x00,
    // Character 50 (0x32) (2)
    // ---------
    // ---------
    // ---------
    // --####---
    // ########-
    // ##----##-
    // ------##-
    // -----##--
    // ----##---
    // --###----
    // -##------
    // ##-------
    // ########-
    // ########-
    // ---------
    // ---------
    0x02, 0x30, 0x03, 0x18, 0x8A, 0x98, 0xF0, 0x70, 0x00, 0x38, 0x3C, 0x36, 0x32, 0x33, 0x31, 0x02,
    0x30, 0x01, 0x00,
    // Character 51 (0x33) (3)
    // ---------
    // ---------
    // ---------
    // --#####--
    // ########-
    // ##----##-
    // ------##-
    // ---####--
    // ---####--
    // ------##-
    // ------##-
    // ##----##-
    // #######--
    // --####---
    // ---------
    // ---------
    0x02, 0x30, 0x81, 0x18, 0x03, 0x98, 0x83, 0xF8, 0x70, 0x00, 0x02, 0x18, 0x81, 0x30, 0x03, 0x31,
    0x83, 0x1F, 0x0E, 0x00,
    // Character 52 (0x34) (4)
    // ---------
    // ---------
    // ---------
    // ----###--
    // ----###--
    // ---####--
    // --##-##--
    // --##-##--
    // -##--##--
    // ##---##--
    // ########-
    // ########-
    // -----##--
    // -----##--
    // ---------
    // ---------
    0x02, 0x00, 0x83, 0xC0, 0xE0, 0x38, 0x02, 0xF8, 0x02, 0x00, 0x83, 0x0E, 0x0F, 0x0D, 0x02, 0x0C,
    0x02, 0x3F, 0x82, 0x0C, 0x00,
    // Character 53 (0x35) (5)
    // ---------
    // ---------
    // ---------
    // #######--
    // #######--
    // ##-------
    // ######---
    // #######--
    // ##---###-
    // ------##-
    // ------##-
    // ##---###-
    // -######--
    // --####---
    // ---------
    // ---------
    0x02, 0xF8, 0x04, 0xD8, 0x81, 0x98, 0x02, 0x00, 0x82, 0x09, 0x19, 0x03, 0x30, 0x84, 0x39, 0x1F,
    0x0F, 0x00,
    // Character 54 (0x36) (6)
    // ---------
    // ---------
    // ---------
    // --#####--
    // -#######-
    // ###---##-
    // ##-------
    // ##-###---
    // ########-
    // ##----##-
    // ##----##-
    // -##---##-
    // -######--
    // --####---
    // ---------
    // ---------
    0x83, 0xE0, 0xF0, 0x38, 0x03, 0x98, 0x86, 0x38, 0x30, 0x00, 0x07, 0x1F, 0x39, 0x03, 0x31, 0x83,
    0x1F, 0x0F, 0x00,
    // Character 55 (0x37) (7)
    // ---------
    // ---------
    // ---------
    // ########-
    // ########-
    // ------##-
    // -----##--
    // ----##---
    // ----##---
    // ---##----
    // ---##----
    // --##-----
    // --##-----
    // --##-----
    // ---------
    // ---------
    0x04, 0x18, 0x84, 0x98, 0xD8, 0x78, 0x38, 0x03, 0x00, 0x84, 0x38, 0x3E, 0x07, 0x01, 0x03, 0x00,
    // Character 56 (0x38) (8)
    // ---------
    // ---------
    // ---------
    // -######--
    // ########-
    // ##----##-
    // ##----##-
    // -######--
    // -######--
    // ##----##-
    // ##----##-
    // ##----##-
    // ########-
    // --####---
    // ---------
    // ---------
    0x82, 0x70, 0xF8, 0x04, 0x98, 0x85, 0xF8, 0x70, 0x00, 0x1E, 0x1F, 0x04, 0x31, 0x83, 0x1F, 0x1E,
    0x00,
    // Character 57 (0x39) (9)
    // ---------
    // ---------
    // ---------
    // --####---
    // -######--
    // ##---###-
    // ##----##-
    // ##----##-
    // -#######-
    // --###-##-
    // ------##-
    // ##---##--
    // #######--
    // -#####---
    // ---------
    // ---------
    0x82, 0xE0, 0xF0, 0x03, 0x18, 0x86, 0x38, 0xF0, 0xE0, 0x00, 0x18, 0x39, 0x03, 0x33, 0x84, 0x39,
    0x1F, 0x07, 0x00,
    // Character 58 (0x3A) (:)
    // ---------
    // ---------
    // ---------
    // ---------
    // ---------
    // ---##----
    // ---##----
    // ---------
    // ---------
    // ---------
    // ---------
    // ---------
    // ---##----
    // ---##----
    // ---------
    // ---------
    0x03, 0x00, 0x02, 0x60, 0x07, 0x00, 0x02, 0x30, 0x04, 0x00,
    // Character 65 (0x41) (A)
    // ----------
    // ----------
    // ----------
    // ----##----
    // ---####---
    // ---####---
    // ---#--#---
    // --##--##--
    // --##--##--
    // --######--
    // -########-
    // -##----##-
    // -##----##-
    // ##------##
    // ----------
    // ----------
    0x02, 0x00, 0x82, 0x80, 0xF0, 0x02, 0x38, 0x82, 0xF0, 0x80, 0x02, 0x00, 0x84, 0x20, 0x3C, 0x1F,
    0x07, 0x02, 0x06, 0x84, 0x07, 0x1F, 0x3C, 0x20,
    // Character 67 (0x43) (C)
    // ---------
    // ---------
    // ---------
    // --####---
    // -######--
    // ###--###-
    // ##----##-
    // ##-------
    // ##-------
    // ##-------
    // ##----##-
    // ###--###-
    // -######--
    // --####---
    // ---------
    // ---------
    0x83, 0xE0, 0xF0, 0x38, 0x02, 0x18, 0x87, 0x38, 0x70, 0x60, 0x00, 0x0F, 0x1F, 0x38, 0x02, 0x30,
    0x84, 0x38, 0x1C, 0x0C, 0x00,
    // Character 68 (0x44) (D)
    // ---------
    // ---------
    // ---------
    // ######---
    // #######--
    // ##---##--
    // ##----##-
    // ##----##-
    // ##----##-
    // ##----##-
    // ##----##-
    // ##---##--
    // #######--
    // ######---
    // ---------
    // ---------
    0x02, 0xF8, 0x03, 0x18, 0x84, 0x38, 0xF0, 0xC0, 0x00, 0x02, 0x3F, 0x03, 0x30, 0x84, 0x38, 0x1F,
    0x07, 0x00,
    // Character 69 (0x45) (E)
    // ---------
    // ---------
    // ---------
    // ########-
    // ########-
    // ##-------
    // ##-------
    // #######--
    // #######--
    // ##-------
    // ##-------
    // ##-------
    // ########-
    // ########-
    // ---------
    // ---------
    0x02, 0xF8, 0x05, 0x98, 0x82, 0x18, 0x00, 0x02, 0x3F, 0x05, 0x31, 0x82, 0x30, 0x00,
    // Character 70 (0x46) (F)
    // ---------
    // ---------
    // ---------
    // ########-
    // ########-
    // ##-------
    // ##-------
    // #######--
    // #######--
    // ##-------
    // ##-------
    // ##-------
    // ##-------
    // ##-------
    // ---------
    // ---------
    0x02, 0xF8, 0x05, 0x98, 0x82, 0x18, 0x00, 0x02, 0x3F, 0x05, 0x01, 0x02, 0x00,
    // Character 71 (0x47) (G)
    // ---------
    // ---------
    // ---------
    // --####---
    // -######--
    // ###--###-
    // ##----##-
    // ##-------
    // ##--####-
    // ##--####-
    // ##----##-
    // -##---##-
    // -#######-
    // --####---
    // ---------
    // ---------
    0x83, 0xE0, 0xF0, 0x38, 0x02, 0x18, 0x88, 0x38, 0x70, 0x60, 0x00, 0x07, 0x1F, 0x38, 0x30, 0x02,
    0x33, 0x02, 0x1F, 0x01, 0x00,
    // Character 72 (0x48) (H)
    // ---------
    // ---------
    // ---------
    // ##----##-
    // ##----##-
    // ##----##-
    // ##----##-
    // ########-
    // ########-
    // ##----##-
    // ##----##-
    // ##----##-
    // ##----##-
    // ##----##-
    // ---------
    // ---------
    0x02, 0xF8, 0x04, 0x80, 0x02, 0xF8, 0x81, 0x00, 0x02, 0x3F, 0x04, 0x01, 0x02, 0x3F, 0x01, 0x00,
    // Character 73 (0x49) (I)
    // ---------
    // ---------
    // ---------
    // ########-
    // ########-
    // ---##----
    // ---##----
    // ---##----
    // ---##----
    // ---##----
    // ---##----
    // ---##----
    // ########-
    // ########-
    // ---------
    // ---------
    0x03, 0x18, 0x02, 0xF8, 0x03, 0x18, 0x81, 0x00, 0x03, 0x30, 0x02, 0x3F, 0x03, 0x30, 0x01, 0x00,
    // Character 75 (0x4B) (K)
    // ---------
    // ---------
    // ---------
    // ##----##-
    // ##---##--
    // ##--##---
    // ##-##----
    // ####-----
    // #####----
    // ######---
    // ##--##---
    // ##---##--
    // ##----##-
    // ##----###
    // ---------
    // ---------
    0x02, 0xF8, 0x87, 0x80, 0xC0, 0x60, 0x30, 0x18, 0x08, 0x00, 0x02, 0x3F, 0x02, 0x03, 0x85, 0x07,
    0x0E, 0x38, 0x30, 0x20,
    // Character 76 (0x4C) (L)
    // ---------
    // ---------
    // ---------
    // ##-------
    // ##-------
    // ##-------
    // ##-------
    // ##-------
    // ##-------
    // ##-------
    // ##-------
    // ##-------
    // ########-
    // ########-
    // ---------
    // ---------
    0x02, 0xF8, 0x07, 0x00, 0x02, 0x3F, 0x06, 0x30, 0x01, 0x00,
    // Character 77 (0x4D) (M)
    // ----------
    // ----------
    // ----------
    // ###---###-
    // ###---###-
    // ####-####-
    // ####-####-
    // ##-#-#-##-
    // ##-#-#-##-
    // ##-###-##-
    // ##--##-##-
    // ##-----##-
    // ##-----##-
    // ##-----##-
    // ----------
    // ----------
    0x02, 0xF8, 0x85, 0x78, 0xE0, 0x00, 0xE0, 0x78, 0x02, 0xF8, 0x81, 0x00, 0x02, 0x3F, 0x85, 0x00,
    0x03, 0x06, 0x07, 0x00, 0x02, 0x3F, 0x01, 0x00,
    // Character 78 (0x4E) (N)
    // ---------
    // ---------
    // ---------
    // ###---##-
    // ###---##-
    // ####--##-
    // ####--##-
    // ##-##-##-
    // ##-##-##-
    // ##-##-##-
    // ##--####-
    // ##--####-
    // ##---###-
    // ##---###-
    // ---------
    // ---------
    0x02, 0xF8, 0x84, 0x78, 0xE0, 0x80, 0x00, 0x02, 0xF8, 0x81, 0x00, 0x02, 0x3F, 0x84, 0x00, 0x03,
    0x0F, 0x3C, 0x02, 0x3F, 0x01, 0x00,
    // Character 79 (0x4F) (O)
    // ---------
    // ---------
    // ---------
    // --####---
    // -######--
    // ###--###-
    // ##----##-
    // ##----##-
    // ##----##-
    // ##----##-
    // ##----##-
    // ###--###-
    // -######--
    // --####---
    // ---------
    // ---------
    0x83, 0xE0, 0xF0, 0x38, 0x02, 0x18, 0x87, 0x38, 0xF0, 0xE0, 0x00, 0x0F, 0x1F, 0x38, 0x02, 0x30,
    0x84, 0x38, 0x1F, 0x0F, 0x00,
    // Character 80 (0x50) (P)
    // ---------
    // ---------
    // ---------
    // ######---
    // #######--
    // ##----##-
    // ##----##-
    // ##----##-
    // #######--
    // ######---
    // ##-------
    // ##-------
    // ##-------
    // ##-------
    // ---------
    // ---------
    0x02, 0xF8, 0x04, 0x18, 0x83, 0xF0, 0xE0, 0x00, 0x02, 0x3F, 0x04, 0x03, 0x81, 0x01, 0x02, 0x00,
    // Character 82 (0x52) (R)
    // ---------
    // ---------
    // ---------
    // ######---
    // ########-
    // ##----##-
    // ##----##-
    // ##----##-
    // #######--
    // #####----
    // ##--##---
    // ##---##--
    // ##----##-
    // ##----###
    // ---------
    // ---------
    0x02, 0xF8, 0x04, 0x18, 0x02, 0xF0, 0x81, 0x00, 0x02, 0x3F, 0x02, 0x03, 0x85, 0x07, 0x0D, 0x39,
    0x30, 0x20,
    // Character 83 (0x53) (S)
    // ---------
    // ---------
    // ---------
    // --####---
    // ########-
    // ##----##-
    // ##-------
    // #####----
    // --#####--
    // -----###-
    // ------##-
    // ##----##-
    // -#######-
    // --####---
    // ---------
    // ---------
    0x02, 0xF0, 0x03, 0x98, 0x81, 0x18, 0x02, 0x30, 0x83, 0x00, 0x08, 0x18, 0x03, 0x31, 0x84, 0x33,
    0x1F, 0x1E, 0x00,
    // Character 84 (0x54) (T)
    // ---------
    // ---------
    // ---------
    // ########-
    // ########-
    // ---##----
    // ---##----
    // ---##----
    // ---##----
    // ---##----
    // ---##----
    // ---##----
    // ---##----
    // ---##----
    // ---------
    // ---------
    0x03, 0x18, 0x02, 0xF8, 0x03, 0x18, 0x04, 0x00, 0x02, 0x3F, 0x04, 0x00,
    // Character 85 (0x55) (U)
    // ---------
    // ---------
    // ---------
    // ##----##-
    // ##----##-
    // ##----##-
    // ##----##-
    // ##----##-
    // ##----##-
    // ##----##-
    // ##----##-
    // ##---###-
    // -######--
    // --####---
    // ---------
    // ---------
    0x02, 0xF8, 0x04, 0x00, 0x02, 0xF8, 0x83, 0x00, 0x0F, 0x1F, 0x03, 0x30, 0x84, 0x38, 0x1F, 0x0F,
    0x00,
    // Character 90 (0x5A) (Z)
    // ---------
    // ---------
    // ---------
    // -#######-
    // -#######-
    // -----##--
    // ----###--
    // ----##---
    // ---##----
    // --##-----
    // -###-----
    // -##------
    // ########-
    // ########-
    // ---------
    // ---------
    0x81, 0x00, 0x03, 0x18, 0x8A, 0xD8, 0xF8, 0x78, 0x18, 0x00, 0x30, 0x3C, 0x3E, 0x37, 0x31, 0x03,
    0x30, 0x01, 0x00,
    // Character 97 (0x61) (a)
    // ----------
    // ----------
    // ----------
    // ----------
    // ----------
    // --#####---
    // -#######--
    // ##----##--
    // --######--
    // ########--
    // ##----##--
    // ##---###--
    // #########-
    // -####--##-
    // ----------
    // ----------
    0x82, 0x80, 0xC0, 0x04, 0x60, 0x82, 0xE0, 0xC0, 0x02, 0x00, 0x82, 0x1E, 0x3E, 0x03, 0x33, 0x85,
    0x1B, 0x1F, 0x3F, 0x30, 0x00,
    // Character 104 (0x68) (h)
    // ---------
    // ---------
    // ##-------
    // ##-------
    // ##-------
    // ##-####--
    // ########-
    // ###---##-
    // ##----##-
    // ##----##-
    // ##----##-
    // ##----##-
    // ##----##-
    // ##----##-
    // ---------
    // ---------
    0x02, 0xFC, 0x81, 0xC0, 0x03, 0x60, 0x83, 0xE0, 0xC0, 0x00, 0x02, 0x3F, 0x04, 0x00, 0x02, 0x3F,
    0x01, 0x00,
    // Character 105 (0x69) (i)
    // ---------
    // ---------
    // ---##----
    // ---##----
    // ---------
    // -####----
    // -####----
    // ---##----
    // ---##----
    // ---##----
    // ---##----
    // ---##----
    // ########-
    // ########-
    // ---------
    // ---------
    0x81, 0x00, 0x02, 0x60, 0x02, 0xEC, 0x04, 0x00, 0x03, 0x30, 0x02, 0x3F, 0x03, 0x30, 0x01, 0x00,
    // Character 109 (0x6D) (m)
    // ---------
    // ---------
    // ---------
    // ---------
    // ---------
    // ####-##--
    // ########-
    // ##-##-##-
    // ##-##-##-
    // ##-##-##-
    // ##-##-##-
    // ##-##-##-
    // ##-##-##-
    // ##-##-##-
    // ---------
    // ---------
    0x02, 0xE0, 0x87, 0x60, 0xE0, 0xC0, 0x60, 0xE0, 0xC0, 0x00, 0x02, 0x3F, 0x81, 0x00, 0x02, 0x3F,
    0x81, 0x00, 0x02, 0x3F, 0x01, 0x00,
    // Character 110 (0x6E) (n)
    // ---------
    // ---------
    // ---------
    // ---------
    // ---------
    // ##-####--
    // ########-
    // ###---##-
    // ##----##-
    // ##----##-
    // ##----##-
    // ##----##-
    // ##----##-
    // ##----##-
    // ---------
    // ---------
    0x02, 0xE0, 0x81, 0xC0, 0x03, 0x60, 0x83, 0xE0, 0xC0, 0x00, 0x02, 0x3F, 0x04, 0x00, 0x02, 0x3F,
    0x01, 0x00,
    // Character 120 (0x78) (x)
    // ---------
    // ---------
    // ---------
    // ---------
    // ---------
    // ###--###-
    // -##--##--
    // --####---
    // --####---
    // ---##----
    // --####---
    // -##--##--
    // -##--##--
    // ##----##-
    // ---------
    // ---------
    0x83, 0x20, 0x60, 0xE0, 0x02, 0x80, 0x87, 0xE0, 0x60, 0x20, 0x00, 0x20, 0x38, 0x1D, 0x02, 0x07,
    0x84, 0x1D, 0x38, 0x20, 0x00,
};
