mattwach/epaper_clock/src/gps_stats_font.c

// Generated font data for gps_stats_font

#include <inttypes.h>
#include <avr/pgmspace.h> 

const uint8_t gps_stats_font[] PROGMEM = {
    0x56, 0x41, 0x52, 0x31,  // id: VAR1
    0x28, // num_chars
    0x01, // height

    // Character offsets
    ' ', 5, 0x00, 0xA0,  // off=160
    '-', 5, 0x00, 0xA2,  // off=162
    '.', 5, 0x00, 0xA6,  // off=166
    '0', 5, 0x00, 0xAB,  // off=171
    '1', 5, 0x00, 0xB1,  // off=177
    '2', 5, 0x00, 0xB7,  // off=183
    '3', 5, 0x00, 0xBD,  // off=189
    '4', 5, 0x00, 0xC3,  // off=195
    '5', 5, 0x00, 0xC9,  // off=201
    '6', 5, 0x00, 0xD0,  // off=208
    '7', 5, 0x00, 0xD7,  // off=215
    '8', 5, 0x00, 0xDD,  // off=221
    '9', 5, 0x00, 0xE4,  // off=228
    ':', 5, 0x00, 0xEB,  // off=235
    'A', 6, 0x00, 0xF0,  // off=240
    'B', 6, 0x00, 0xF7,  // off=247
    'C', 6, 0x00, 0xFF,  // off=255
    'D', 5, 0x01, 0x07,  // off=263
    'E', 5, 0x01, 0x0E,  // off=270
    'F', 5, 0x01, 0x14,  // off=276
    'G', 5, 0x01, 0x1A,  // off=282
    'H', 5, 0x01, 0x20,  // off=288
    'I', 5, 0x01, 0x27,  // off=295
    'J', 5, 0x01, 0x2D,  // off=301
    'K', 6, 0x01, 0x33,  // off=307
    'L', 5, 0x01, 0x3A,  // off=314
    'M', 5, 0x01, 0x40,  // off=320
    'N', 5, 0x01, 0x46,  // off=326
    'O', 5, 0x01, 0x4C,  // off=332
    'P', 5, 0x01, 0x53,  // off=339
    'Q', 5, 0x01, 0x5A,  // off=346
    'R', 6, 0x01, 0x61,  // off=353
    'S', 5, 0x01, 0x68,  // off=360
    'T', 6, 0x01, 0x6F,  // off=367
    'U', 5, 0x01, 0x77,  // off=375
    'V', 6, 0x01, 0x7E,  // off=382
    'W', 6, 0x01, 0x85,  // off=389
    'X', 6, 0x01, 0x8C,  // off=396
    'Y', 6, 0x01, 0x93,  // off=403
    'Z', 6, 0x01, 0x9A,  // off=410
    // Character data
    // Character 32 (0x20) ( )
    // -----
    // -----
    // -----
    // -----
    // -----
    // -----
    // -----
    // -----
    0x05, 0x00,
    // Character 45 (0x2D) (-)
    // -----
    // -----
    // -----
    // -----
    // -----
    // ###--
    // -----
    // -----
    0x03, 0x20, 0x02, 0x00,
    // Character 46 (0x2E) (.)
    // -----
    // -----
    // -----
    // -----
    // -----
    // -----
    // -----
    // -#---
    0x82, 0x00, 0x80, 0x03, 0x00,
    // Character 48 (0x30) (0)
    // -----
    // -##--
    // #--#-
    // #--#-
    // ##-#-
    // #--#-
    // #--#-
    // -##--
    0x85, 0x7C, 0x92, 0x82, 0x7C, 0x00,
    // Character 49 (0x31) (1)
    // -----
    // --#--
    // -##--
    // --#--
    // --#--
    // --#--
    // --#--
    // -###-
    0x85, 0x00, 0x84, 0xFE, 0x80, 0x00,
    // Character 50 (0x32) (2)
    // -----
    // -##--
    // #--#-
    // ---#-
    // --#--
    // -#---
    // #----
    // ####-
    0x85, 0xC4, 0xA2, 0x92, 0x8C, 0x00,
    // Character 51 (0x33) (3)
    // -----
    // -##--
    // #--#-
    // ---#-
    // --#--
    // ---#-
    // #--#-
    // -##--
    0x85, 0x44, 0x82, 0x92, 0x6C, 0x00,
    // Character 52 (0x34) (4)
    // -----
    // ---#-
    // --##-
    // -#-#-
    // #--#-
    // #####
    // ---#-
    // ---#-
    0x85, 0x30, 0x28, 0x24, 0xFE, 0x20,
    // Character 53 (0x35) (5)
    // -----
    // ####-
    // #----
    // ###--
    // ---#-
    // ---#-
    // #--#-
    // -##--
    0x81, 0x4E, 0x02, 0x8A, 0x82, 0x72, 0x00,
    // Character 54 (0x36) (6)
    // -----
    // -###-
    // #----
    // ###--
    // #--#-
    // #--#-
    // #--#-
    // -##--
    0x81, 0x7C, 0x02, 0x8A, 0x82, 0x72, 0x00,
    // Character 55 (0x37) (7)
    // -----
    // ####-
    // ---#-
    // --#--
    // --#--
    // -#---
    // -#---
    // -#---
    0x85, 0x02, 0xE2, 0x1A, 0x06, 0x00,
    // Character 56 (0x38) (8)
    // -----
    // -##--
    // #--#-
    // #--#-
    // -##--
    // #--#-
    // #--#-
    // -##--
    0x81, 0x6C, 0x02, 0x92, 0x82, 0x6C, 0x00,
    // Character 57 (0x39) (9)
    // -----
    // -##--
    // #--#-
    // #--#-
    // -###-
    // ---#-
    // ---#-
    // ###--
    0x81, 0x8C, 0x02, 0x92, 0x82, 0x7C, 0x00,
    // Character 58 (0x3A) (:)
    // -----
    // -----
    // -----
    // -#---
    // -----
    // -----
    // -----
    // -#---
    0x82, 0x00, 0x88, 0x03, 0x00,
    // Character 65 (0x41) (A)
    // ------
    // --#---
    // -#-#--
    // -#-#--
    // -#-#--
    // -###--
    // #---#-
    // #---#-
    0x86, 0xC0, 0x3C, 0x22, 0x3C, 0xC0, 0x00,
    // Character 66 (0x42) (B)
    // ------
    // ###---
    // #--#--
    // #--#--
    // ###---
    // #--#--
    // #--#--
    // ###---
    0x81, 0xFE, 0x02, 0x92, 0x81, 0x6C, 0x02, 0x00,
    // Character 67 (0x43) (C)
    // ------
    // -##---
    // #--#--
    // #-----
    // #-----
    // #-----
    // #--#--
    // -##---
    0x81, 0x7C, 0x02, 0x82, 0x81, 0x44, 0x02, 0x00,
    // Character 68 (0x44) (D)
    // -----
    // ###--
    // #--#-
    // #--#-
    // #--#-
    // #--#-
    // #--#-
    // ###--
    0x81, 0xFE, 0x02, 0x82, 0x82, 0x7C, 0x00,
    // Character 69 (0x45) (E)
    // -----
    // ####-
    // #----
    // #----
    // ####-
    // #----
    // #----
    // ####-
    0x81, 0xFE, 0x03, 0x92, 0x01, 0x00,
    // Character 70 (0x46) (F)
    // -----
    // ####-
    // #----
    // #----
    // ####-
    // #----
    // #----
    // #----
    0x81, 0xFE, 0x03, 0x12, 0x01, 0x00,
    // Character 71 (0x47) (G)
    // -----
    // -##--
    // #--#-
    // #----
    // #-##-
    // #--#-
    // #--#-
    // -##--
    0x85, 0x7C, 0x82, 0x92, 0x74, 0x00,
    // Character 72 (0x48) (H)
    // -----
    // #--#-
    // #--#-
    // #--#-
    // ####-
    // #--#-
    // #--#-
    // #--#-
    0x81, 0xFE, 0x02, 0x10, 0x82, 0xFE, 0x00,
    // Character 73 (0x49) (I)
    // -----
    // -###-
    // --#--
    // --#--
    // --#--
    // --#--
    // --#--
    // -###-
    0x85, 0x00, 0x82, 0xFE, 0x82, 0x00,
    // Character 74 (0x4A) (J)
    // -----
    // --##-
    // ---#-
    // ---#-
    // ---#-
    // ---#-
    // #--#-
    // -##--
    0x85, 0x40, 0x80, 0x82, 0x7E, 0x00,
    // Character 75 (0x4B) (K)
    // ------
    // #--#--
    // #-#---
    // #-#---
    // ##----
    // #-#---
    // #-#---
    // #--#--
    0x84, 0xFE, 0x10, 0x6C, 0x82, 0x02, 0x00,
    // Character 76 (0x4C) (L)
    // -----
    // #----
    // #----
    // #----
    // #----
    // #----
    // #----
    // ####-
    0x81, 0xFE, 0x03, 0x80, 0x01, 0x00,
    // Character 77 (0x4D) (M)
    // -----
    // #---#
    // ##-##
    // ##-##
    // #-#-#
    // #-#-#
    // #---#
    // #---#
    0x85, 0xFE, 0x0C, 0x30, 0x0C, 0xFE,
    // Character 78 (0x4E) (N)
    // -----
    // #--#-
    // ##-#-
    // ##-#-
    // #-##-
    // #-##-
    // #--#-
    // #--#-
    0x85, 0xFE, 0x0C, 0x30, 0xFE, 0x00,
    // Character 79 (0x4F) (O)
    // -----
    // -##--
    // #--#-
    // #--#-
    // #--#-
    // #--#-
    // #--#-
    // -##--
    0x81, 0x7C, 0x02, 0x82, 0x82, 0x7C, 0x00,
    // Character 80 (0x50) (P)
    // -----
    // ###--
    // #--#-
    // #--#-
    // ###--
    // #----
    // #----
    // #----
    0x81, 0xFE, 0x02, 0x12, 0x82, 0x0C, 0x00,
    // Character 81 (0x51) (Q)
    // -----
    // -##--
    // #--#-
    // #--#-
    // #--#-
    // #--#-
    // #--#-
    // -##--
    0x81, 0x7C, 0x02, 0x82, 0x82, 0x7C, 0x00,
    // Character 82 (0x52) (R)
    // ------
    // ###---
    // #--#--
    // #--#--
    // ###---
    // #-#---
    // #--#--
    // #--#--
    0x84, 0xFE, 0x12, 0x32, 0xCC, 0x02, 0x00,
    // Character 83 (0x53) (S)
    // -----
    // -##--
    // #--#-
    // #----
    // -##--
    // ---#-
    // #--#-
    // -##--
    0x81, 0x4C, 0x02, 0x92, 0x82, 0x64, 0x00,
    // Character 84 (0x54) (T)
    // ------
    // #####-
    // --#---
    // --#---
    // --#---
    // --#---
    // --#---
    // --#---
    0x02, 0x02, 0x81, 0xFE, 0x02, 0x02, 0x01, 0x00,
    // Character 85 (0x55) (U)
    // -----
    // #--#-
    // #--#-
    // #--#-
    // #--#-
    // #--#-
    // #--#-
    // -##--
    0x81, 0x7E, 0x02, 0x80, 0x82, 0x7E, 0x00,
    // Character 86 (0x56) (V)
    // ------
    // #---#-
    // #---#-
    // -#-#--
    // -#-#--
    // -#-#--
    // -#-#--
    // --#---
    0x86, 0x06, 0x78, 0x80, 0x78, 0x06, 0x00,
    // Character 87 (0x57) (W)
    // ------
    // #---#-
    // #---#-
    // #-#-#-
    // #-#-#-
    // -#-#--
    // -#-#--
    // -#-#--
    0x86, 0x1E, 0xE0, 0x18, 0xE0, 0x1E, 0x00,
    // Character 88 (0x58) (X)
    // ------
    // #---#-
    // -#-#--
    // -#-#--
    // --#---
    // -#-#--
    // -#-#--
    // #---#-
    0x86, 0x82, 0x6C, 0x10, 0x6C, 0x82, 0x00,
    // Character 89 (0x59) (Y)
    // ------
    // #---#-
    // -#-#--
    // -#-#--
    // --#---
    // --#---
    // --#---
    // --#---
    0x86, 0x02, 0x0C, 0xF0, 0x0C, 0x02, 0x00,
    // Character 90 (0x5A) (Z)
    // ------
    // ####--
    // ---#--
    // --#---
    // -#----
    // -#----
    // #-----
    // ####--
    0x84, 0xC2, 0xB2, 0x8A, 0x86, 0x02, 0x00,
};
