mattwach/epaper_clock/src/clock_number_font.h

#ifndef CLOCK_NUMBER_FONT_H
#define CLOCK_NUMBER_FONT_H
// Generated font data for clock_number_font.yaml

#include <inttypes.h>
#include <avr/pgmspace.h>

extern const uint8_t clock_number_font[] PROGMEM;

#endif  // CLOCK_NUMBER_FONT_H
