mattwach/epaper_clock/src/detail_numbers_font.h

#ifndef DETAIL_NUMBERS_FONT_H
#define DETAIL_NUMBERS_FONT_H
// Generated font data for detail_numbers_font.yaml

#include <inttypes.h>
#include <avr/pgmspace.h>

extern const uint8_t detail_numbers_font[] PROGMEM;

#endif  // DETAIL_NUMBERS_FONT_H
