mattwach/epaper_clock/src/gps_stats_font.h

#ifndef GPS_STATS_FONT_H
#define GPS_STATS_FONT_H
// Generated font data for gps_stats_font.yaml

#include <inttypes.h>
#include <avr/pgmspace.h>

extern const uint8_t gps_stats_font[] PROGMEM;

#endif  // GPS_STATS_FONT_H
