mattwach/epaper_clock/src/labels_font.h

#ifndef LABELS_FONT_H
#define LABELS_FONT_H
// Generated font data for labels_font.yaml

#include <inttypes.h>
#include <avr/pgmspace.h>

extern const uint8_t labels_font[] PROGMEM;

#endif  // LABELS_FONT_H
