mattwach/epaper_clock/src/pressure_font.h

#ifndef PRESSURE_FONT_H
#define PRESSURE_FONT_H
// Generated font data for pressure_font.yaml

#include <inttypes.h>
#include <avr/pgmspace.h>

extern const uint8_t pressure_font[] PROGMEM;

#endif  // PRESSURE_FONT_H
